ngdrascal/jbecrtctrl/docs/schema/JBE_CRT_Controller/Page2.kicad_sch

## KiCad design docs/schema/JBE_CRT_Controller/Page2.kicad_sch (2026-04-16, an earlier design)

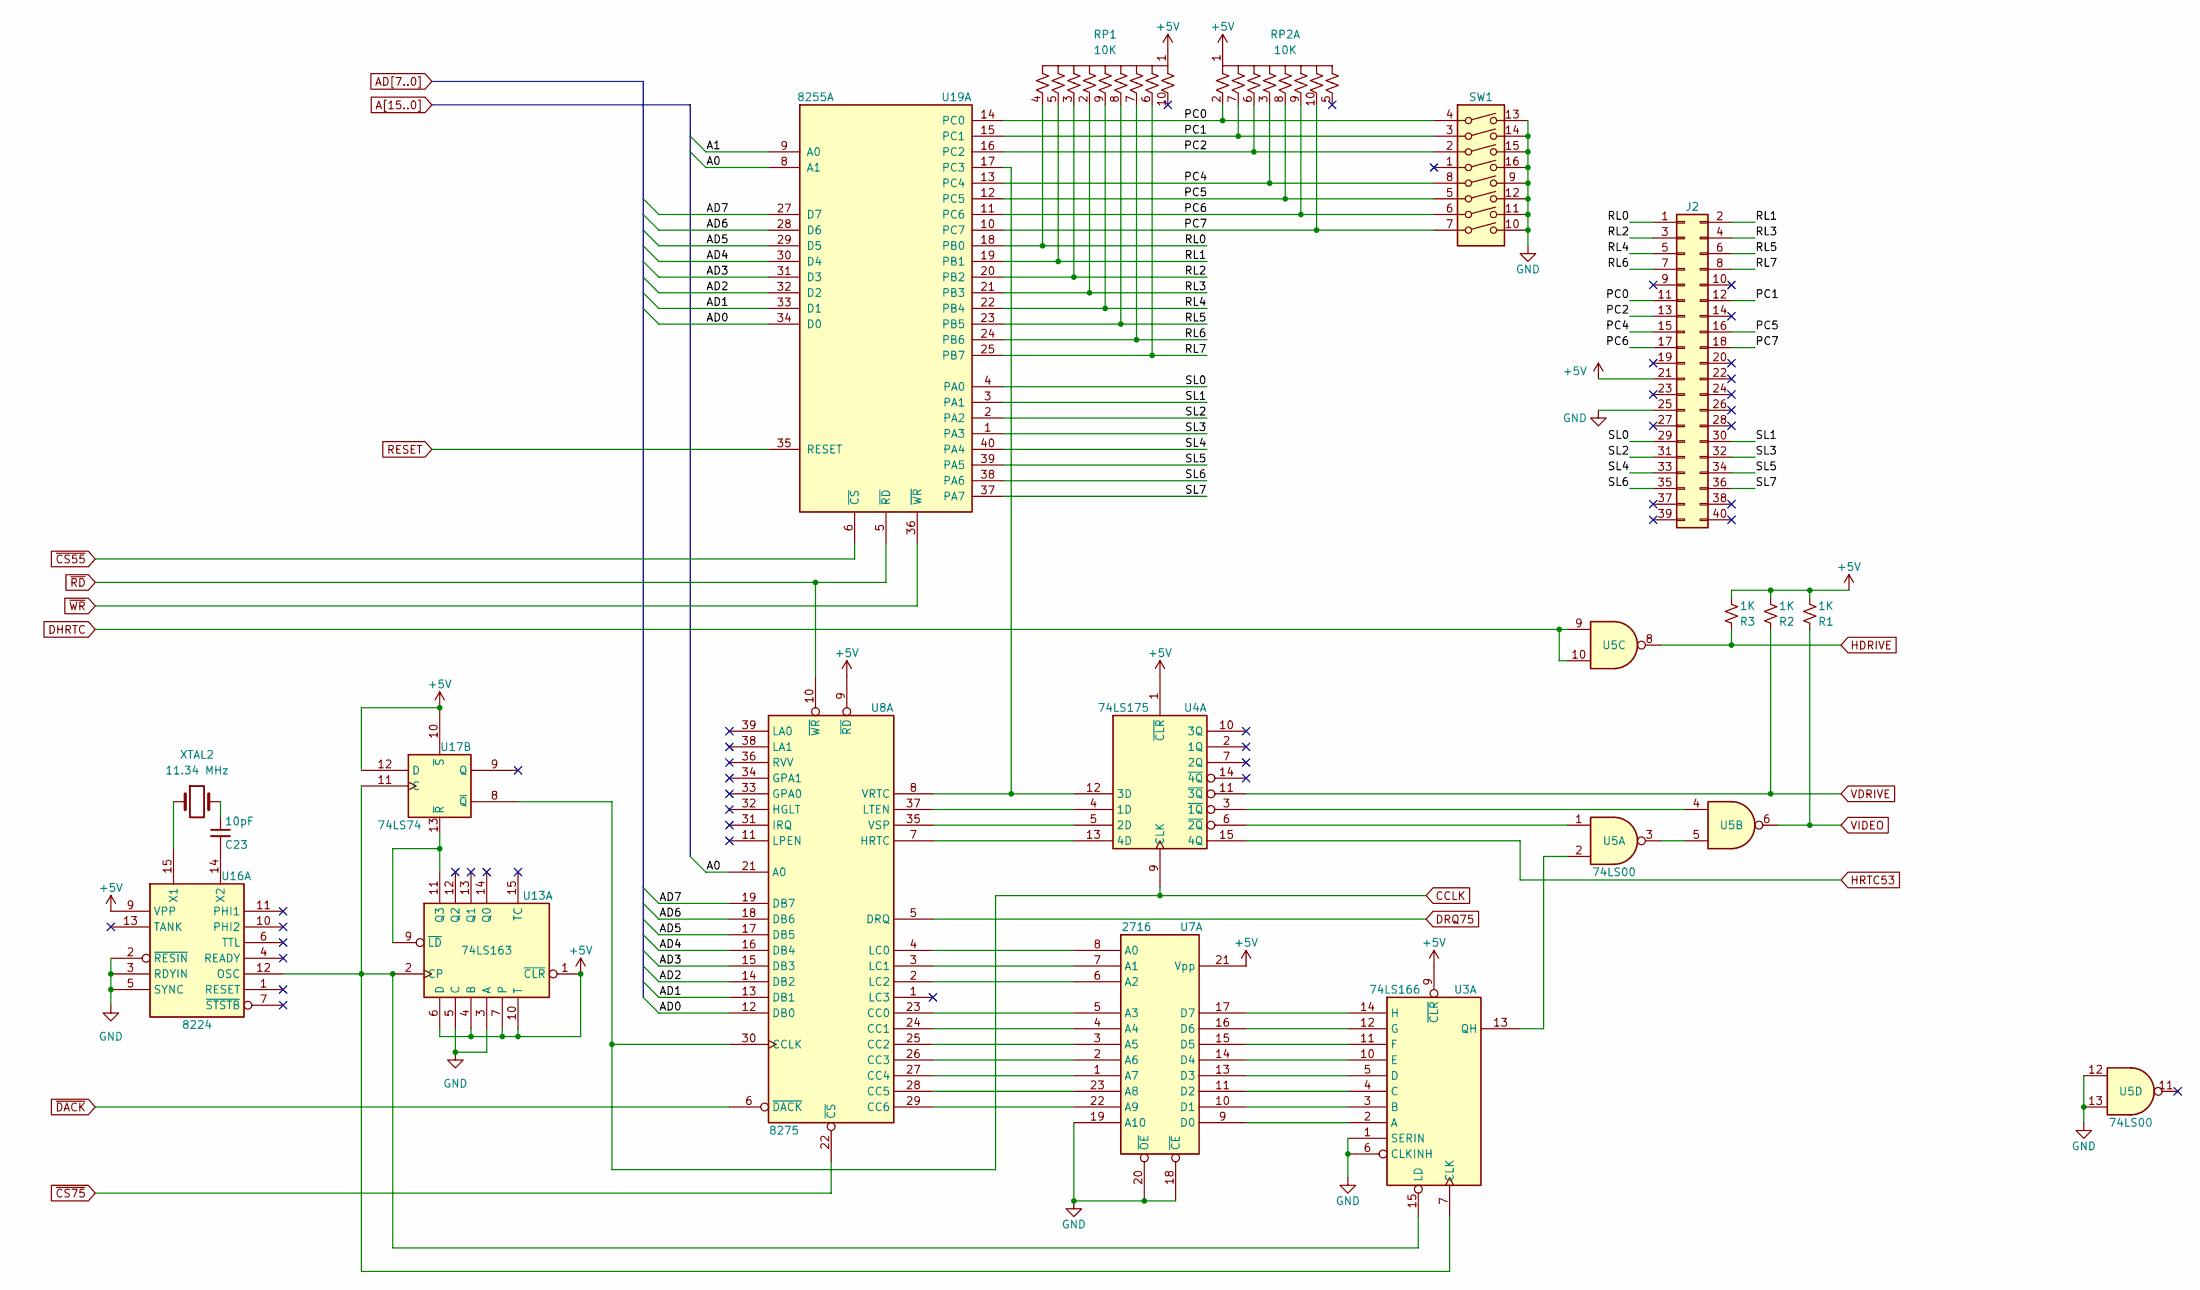
[picture p8: schematic Page2.kicad_sch]

Parts:
C23: 10pF
J2: Conn_02x20_Odd_Even
R1, R2, R3: 1K
RP1, RP2: 10K
SW1: SW_DIP_x08
U3: 74LS166
U4: 74LS175
U5: 74LS00
U7: 2716
U8: 8275
U13: 74LS163
U16: 8224; DIP-16_W7.62mm
U17: 74LS74
U19: 8255A; DIP-40_W15.24mm
XTAL2: 11.34 MHz

Connections:
+5V: J2.21, R1.1, R2.1, R3.1, RP1.1, RP2.1, U3.9 (~CLR), U4.1 (~CLR), U7.21 (Vpp), U8.9 (~RD), U13.1 (~CLR), U13.4 (B), U13.6 (D), U13.7, U13.10 (T), U16.9 (VPP), U17.10 (~S), U17.12 (D)
A0: U8.21 (A0), U19.8 (A1)
A1: U19.9 (A0)
AD0: U8.12 (DB0), U19.34 (D0)
AD1: U8.13 (DB1), U19.33 (D1)
AD2: U8.14 (DB2), U19.32 (D2)
AD3: U8.15 (DB3), U19.31 (D3)
AD4: U8.16 (DB4), U19.30 (D4)
AD5: U8.17 (DB5), U19.29 (D5)
AD6: U8.18 (DB6), U19.28 (D6)
AD7: U8.19 (DB7), U19.27 (D7)
CCLK: U4.9 (CLK), U8.30 (CCLK), U17.8 (~Q)
DHRTC: U5.9, U5.10
DRQ75: U8.5 (DRQ)
GND: J2.25, SW1.9, SW1.10, SW1.11, SW1.12, SW1.13, SW1.14, SW1.15, SW1.16, U3.1 (SERIN), U3.6 (CLKINH), U5.12, U5.13, U7.18 (~CE), U7.19 (A10), U7.20 (~OE), U13.3 (A), U13.5 (C), U16.2 (~RESIN), U16.3 (RDYIN), U16.5 (SYNC)
HDRIVE: R3.2, U5.8
HRTC53: U4.15 (4Q)
unnamed: C23.1, XTAL2.2
unnamed: C23.2, U16.14 (X2)
unnamed: U3.2 (A), U7.9 (D0)
unnamed: U3.3 (B), U7.10 (D1)
unnamed: U3.4 (C), U7.11 (D2)
unnamed: U3.5 (D), U7.13 (D3)
unnamed: U3.10 (E), U7.14 (D4)
unnamed: U3.11 (F), U7.15 (D5)
unnamed: U3.12 (G), U7.16 (D6)
unnamed: U3.13 (QH), U5.2
unnamed: U3.14 (H), U7.17 (D7)
unnamed: U4.3 (~1Q), U5.4
unnamed: U4.4 (1D), U8.37 (LTEN)
unnamed: U4.5 (2D), U8.35 (VSP)
unnamed: U4.6 (~2Q), U5.1
unnamed: U4.13 (4D), U8.7 (HRTC)
unnamed: U5.3, U5.5
unnamed: U7.1 (A7), U8.27 (CC4)
unnamed: U7.2 (A6), U8.26 (CC3)
unnamed: U7.3 (A5), U8.25 (CC2)
unnamed: U7.4 (A4), U8.24 (CC1)
unnamed: U7.5 (A3), U8.23 (CC0)
unnamed: U7.6 (A2), U8.2 (LC2)
unnamed: U7.7 (A1), U8.3 (LC1)
unnamed: U7.8 (A0), U8.4 (LC0)
unnamed: U7.22 (A9), U8.29 (CC6)
unnamed: U7.23 (A8), U8.28 (CC5)
unnamed: U3.7 (CLK), U3.15 (LD), U13.2 (CP), U16.12 (OSC), U17.11 (C)
unnamed: U13.9 (~LD), U13.11 (Q3), U17.13 (~R)
unnamed: U16.15 (X1), XTAL2.1
unnamed: U4.12 (3D), U8.8 (VRTC), U19.17 (PC3)
PC0: J2.11, RP2.2, SW1.4, U19.14 (PC0)
PC1: J2.12, RP2.7, SW1.3, U19.15 (PC1)
PC2: J2.13, RP2.6, SW1.2, U19.16 (PC2)
PC4: J2.15, RP2.3, SW1.8, U19.13 (PC4)
PC5: J2.16, RP2.8, SW1.5, U19.12 (PC5)
PC6: J2.17, RP2.9, SW1.6, U19.11 (PC6)
PC7: J2.18, RP2.10, SW1.7, U19.10 (PC7)
RESET: U19.35 (RESET)
RL0: J2.1, RP1.4, U19.18 (PB0)
RL1: J2.2, RP1.5, U19.19 (PB1)
RL2: J2.3, RP1.3, U19.20 (PB2)
RL3: J2.4, RP1.2, U19.21 (PB3)
RL4: J2.5, RP1.9, U19.22 (PB4)
RL5: J2.6, RP1.8, U19.23 (PB5)
RL6: J2.7, RP1.7, U19.24 (PB6)
RL7: J2.8, RP1.6, U19.25 (PB7)
SL0: J2.29, U19.4 (PA0)
SL1: J2.30, U19.3 (PA1)
SL2: J2.31, U19.2 (PA2)
SL3: J2.32, U19.1 (PA3)
SL4: J2.33, U19.40 (PA4)
SL5: J2.34, U19.39 (PA5)
SL6: J2.35, U19.38 (PA6)
SL7: J2.36, U19.37 (PA7)
VDRIVE: R2.2, U4.11 (~3Q)
VIDEO: R1.2, U5.6
~CS55: U19.6 (~CS)
~CS75: U8.22 (~CS)
~DACK: U8.6 (~DACK)
~RD: U8.10 (~WR), U19.5 (~RD)
~WR: U19.36 (~WR)
