ngdrascal/jbecrtctrl/src/ChrGen.asm

;FILENAME CHRGEN.SRC CREATED 30 JAN 1980 BY TOM ROSSI
;THIS FILE CONTAINS THE DOT PATTERNS FOR THE. LOW-COST
;8275 CRT DEMO BOARDS.
OASC00: DB      00000000B       ; NUL
        DB      00000000B
        DB      00000000B
        DB      00000000B
        DB      00000000B
        DB      00000000B
        DB      00000000B
        DB      00000000B
ASC01:  DB      00000000B       ; SOH
        DB      00000000B
        DB      00000000B
        DB      00000000B
        DB      00000000B
        DB      00000000B
        DB      00000000B
        DB      00000000B
ASC02:  DB      00000000B       ; STX
        DB      00000000B
        DB      00000000B
        DB      00000000B
        DB      00000000B
        DB      00000000B
        DB      00000000B
        DB      00000000B
ASC03:  DB      00000000B       ; ETX
        DB      00000000B
        DB      00000000B
        DB      00000000B
        DB      00000000B
        DB      00000000B
        DB      00000000B
        DB      00000000B
ASC04:  DB      00000000B       ; EOT
        DB      00000000B
        DB      00000000B
        DB      00000000B
        DB      00000000B
        DB      00000000B
        DB      00000000B
        DB      00000000B
ASC05:  DB      00000000B       ; ENQ
        DB      00000000B
        DB      00000000B
        DB      00000000B
        DB      00000000B
        DB      00000000B
        DB      00000000B
        DB      00000000B
ASC06:  DB      00000000B       ; ACK
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
        DB      00000000B
        DB      00000000B
        DB      00000000B
ASC7F:  DB      00000000B       ; DEL
        DB      00000000B
        DB      00000000B
        DB      00000000B
        DB      00000000B
        DB      00000000B
        DB      00000000B
        DB      00000000B
